ashtorak/CanSeeNoiseGen/Hardware/20210617_202601.jpg

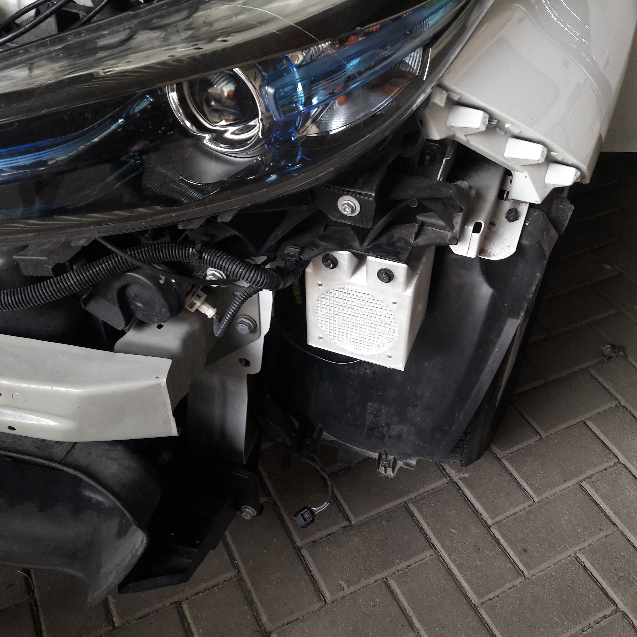
Hardware/20210617_202601.jpg
