ashtorak/CanSeeNoiseGen/Hardware/20210617_202718.jpg

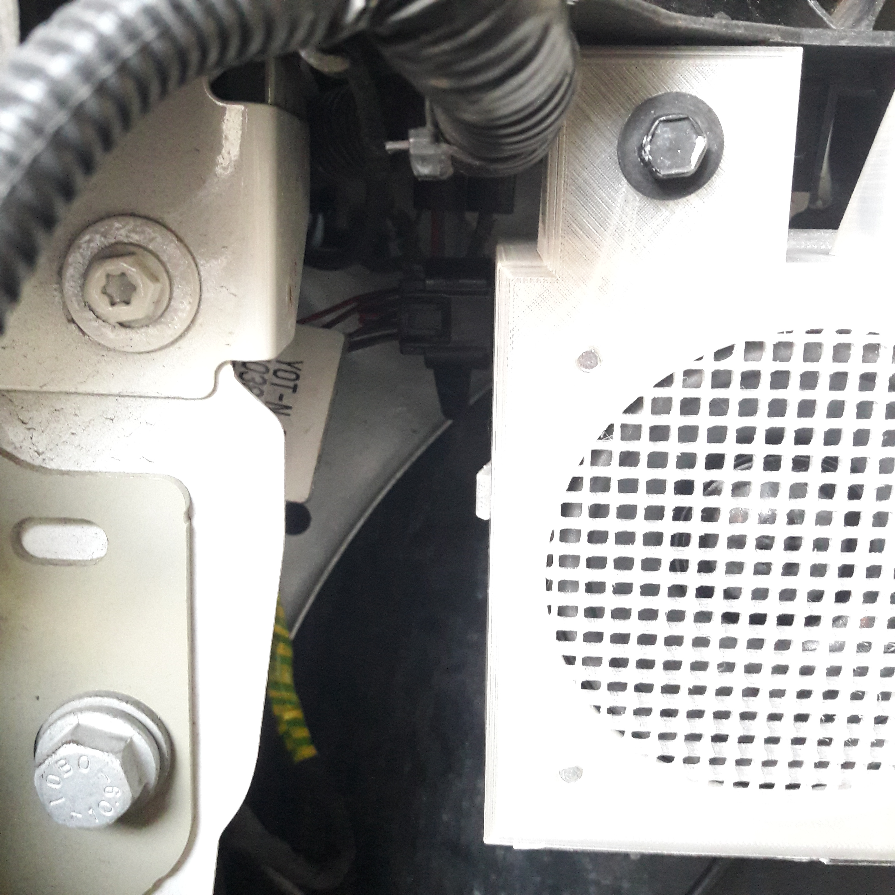
Hardware/20210617_202718.jpg
