ashtorak/CanSeeNoiseGen/include/config.h

#ifndef _CONFIG_H_
#define _CONFIG_H_

#include <EEPROM.h>

#define WIFI_STATION 1
#define WIFI_SOFTAP  2

#define DEBUG_COMMAND_FF      0x08
#define DEBUG_COMMAND         0x04
#define DEBUG_BUS_RECEIVE_FF  0x01
#define DEBUG_COMMAND_ISO     0x10

// Config ********************************************************************
// structure that defines the firmware's configuration
typedef struct {
  uint32_t magicnumber;                    // does that read CanSee?
  byte version;
  byte mode_serial;
  byte mode_bluetooth;
  byte mode_wifi;
  byte mode_debug;
  char name_bluetooth [32];
  char pin_bluetooth [8];
  char ssid_ap [32];
  char password_ap [16];
  char ssid_station [32];
  char password_station [16];
  byte can0_rx;
  byte can0_tx;
  uint16_t can0_speed;
  byte can1_rx;
  byte can1_tx;
  uint16_t can1_speed;
  //** past this line will NOT be initialized by EEPROM but it global data
  uint8_t bus;
  void (*command_handler)();                       // command handler
  void (*output_handler)(String o);                // output handler
  uint16_t boot_count;
} CS_CONFIG_t;

CS_CONFIG_t *getConfig ();
void setConfigToEeprom (bool reset);

#endif
