ashtorak/CanSeeNoiseGen/include/isotphandler.h

#ifndef _ISOTPHANDLER_H_
#define _ISOTPHANDLER_H_

#include <Arduino.h>

#include "config.h"
#include "canhandler.h"
#include "utils.h"
#include "zoe.h"

#define DEBUG_COMMAND         0x04
#define DEBUG_BUS_RECEIVE_ISO 0x02

// see https://en.wikipedia.org/wiki/ISO_15765-2 for ISO-TP

// ISO-TP message ************************************************************
typedef struct {
  uint32_t id = 0xffffffff;                        // the from-address of the responding device
  uint16_t length = 0;                             // size, max 4096
  uint16_t index = 0;                              // pointer
  uint8_t next = 1;                                // sequence of next frame
  uint8_t data[4096];                              // max ISOTP multiframe message
  unsigned long flow_delay = 0;                    // delay between outgoing isoMessageToString
  uint8_t flow_counter = 0;                        // frames to send (until new flow control)
  uint8_t flow_active = 0;                         // 0=no, 1=yes
} ISO_MESSAGE_t;

void isotp_init ();
void isotp_ticker ();
void storeIsotpframe (CAN_frame_t &frame, uint8_t bus);
String isoMessageToString (ISO_MESSAGE_t &message);
void can_send_flow (uint32_t requestId, uint8_t flow);
void requestIsotp (uint32_t id, int16_t length, uint8_t *request, uint8_t bus);
String isoMessageToString (ISO_MESSAGE_t &message);

#endif
