ashtorak/CanSeeNoiseGen/src/utils.cpp

#include "utils.h"
// Utility functions *********************************************************

String getHexSimple(uint8_t num)
{
  String stringOne = String(num, HEX);
  return stringOne;
}

String getHex(uint32_t num)
{
  String stringOne = String(num, HEX);
  if (stringOne.length() < 2)
    stringOne = "0" + stringOne;
  return stringOne;
}

uint32_t hexToDec(String hexString)
{
  uint32_t decValue = 0;
  int nextInt;

  for (int i = 0; i < hexString.length(); i++)
  {
    nextInt = int(hexString.charAt(i));
    if (nextInt >= 48 && nextInt <= 57)
      nextInt = map(nextInt, 48, 57, 0, 9);
    else if (nextInt >= 65 && nextInt <= 70)
      nextInt = map(nextInt, 65, 70, 10, 15);
    else if (nextInt >= 97 && nextInt <= 102)
      nextInt = map(nextInt, 97, 102, 10, 15);
    nextInt = constrain(nextInt, 0, 15);
    decValue = (decValue * 16) + nextInt;
  }
  return decValue;
}
