ashtorak/CanSeeNoiseGen/Hardware/20210617_200722.jpg

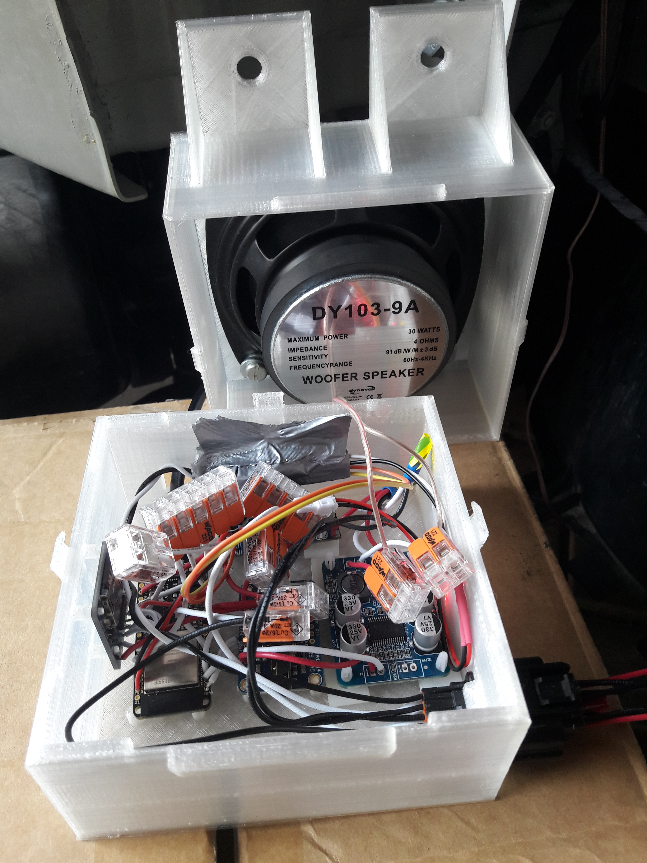
Hardware/20210617_200722.jpg
